AmmarPL/Outdoor-Air-Pollution/Presentation/Inverse_Distance_Plots/Final/NO2.JPG

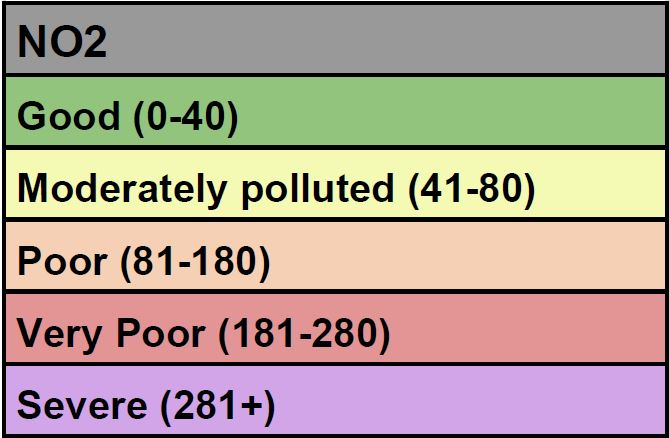
Presentation/Inverse_Distance_Plots/Final/NO2.JPG
