AmmarPL/Outdoor-Air-Pollution/Circuit/Circuit_Diagram.png

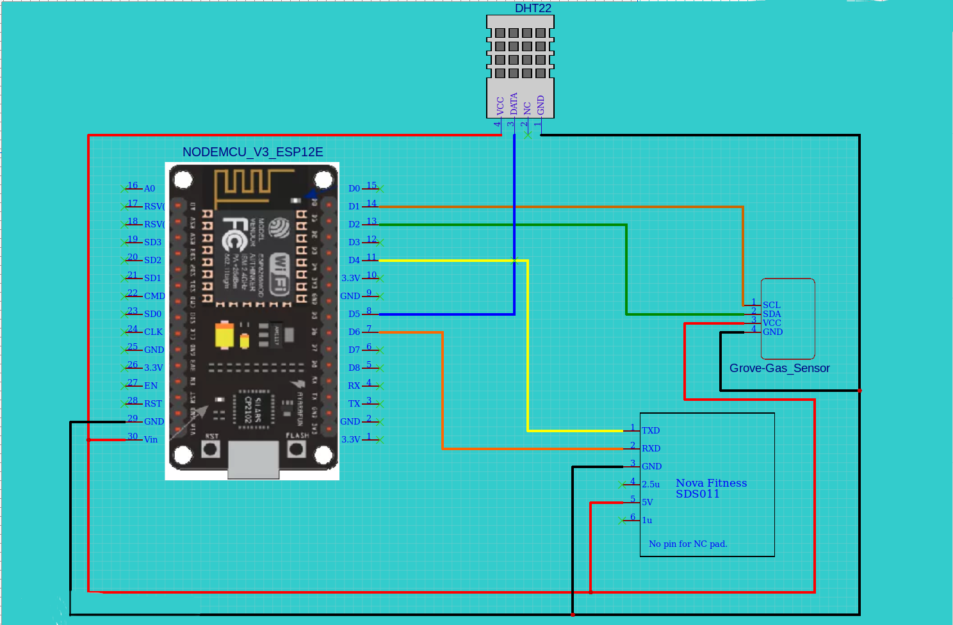
Circuit/Circuit_Diagram.png
