AmmarPL/Outdoor-Air-Pollution/Presentation/.picasaoriginals/Map.jpg

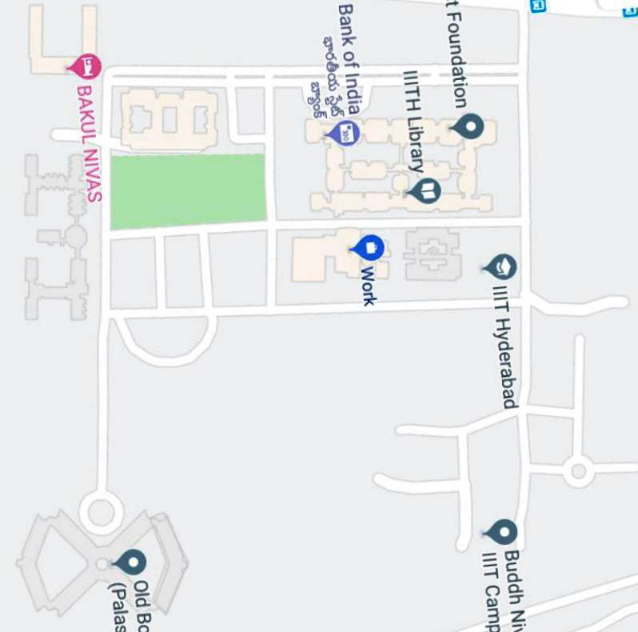
Presentation/.picasaoriginals/Map.jpg
