AmmarPL/Outdoor-Air-Pollution/Presentation/Comparison_Plots/CO.png

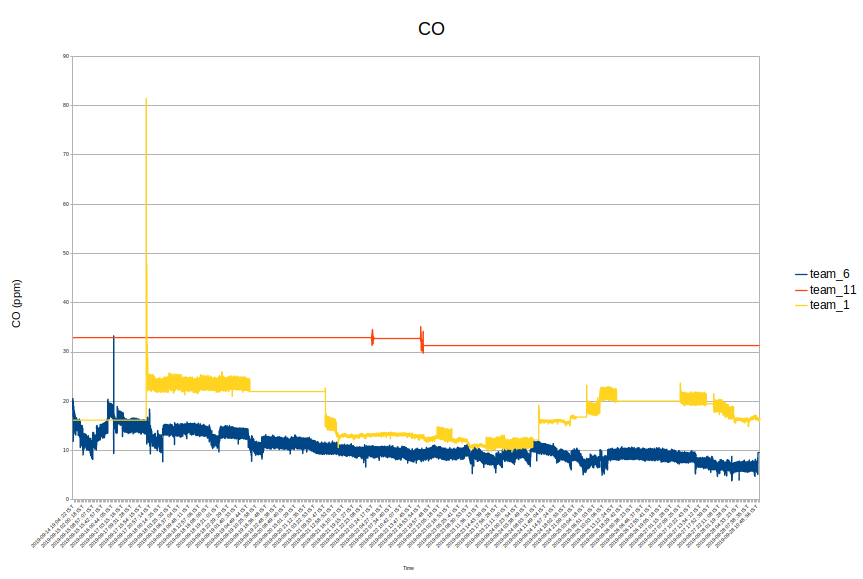
Presentation/Comparison_Plots/CO.png
