AmmarPL/Outdoor-Air-Pollution/Presentation/Comparison_Plots/Humidity.png

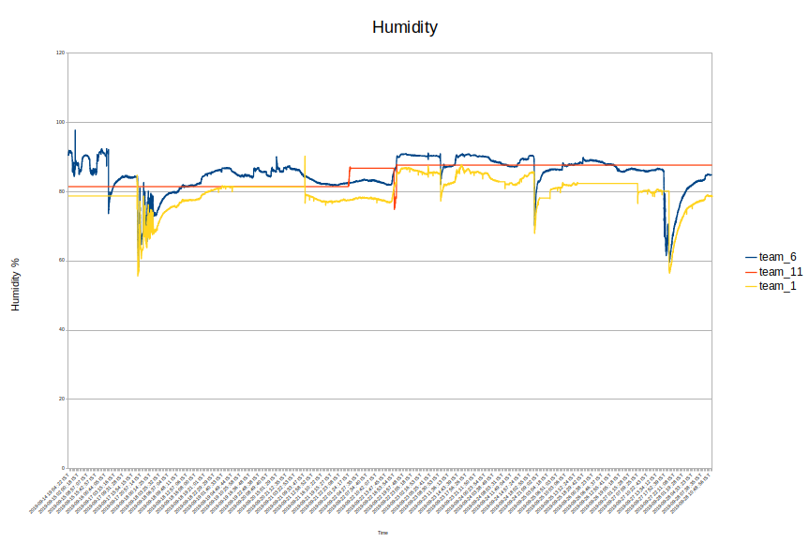
Presentation/Comparison_Plots/Humidity.png
