AmmarPL/Outdoor-Air-Pollution/Presentation/Comparison_Plots/NH3.png

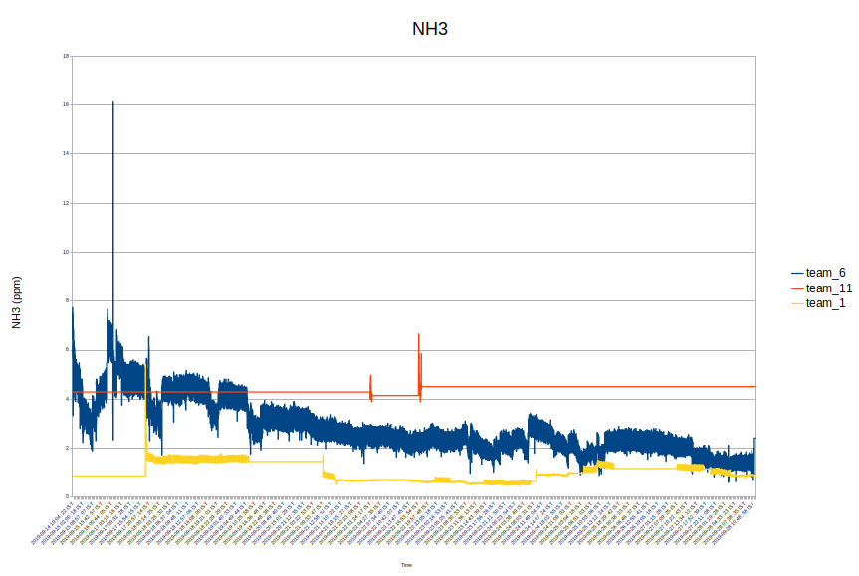
Presentation/Comparison_Plots/NH3.png
