AmmarPL/Outdoor-Air-Pollution/Presentation/Comparison_Plots/NO2.png

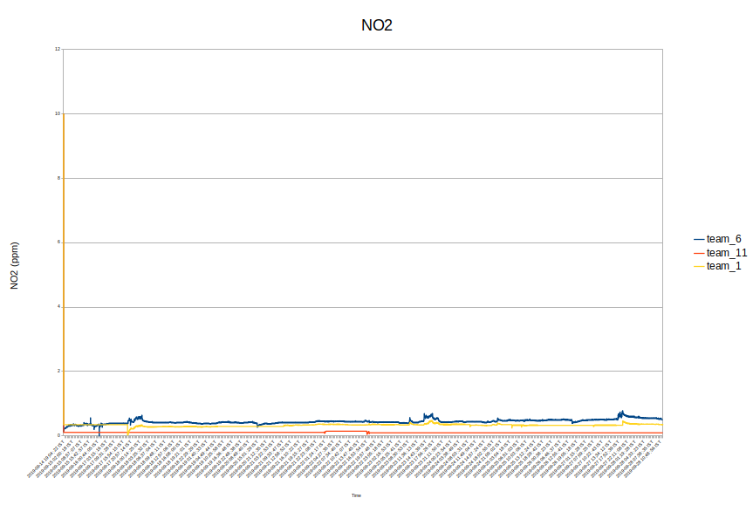
Presentation/Comparison_Plots/NO2.png
