AmmarPL/Outdoor-Air-Pollution/Presentation/Comparison_Plots/Pm25.png

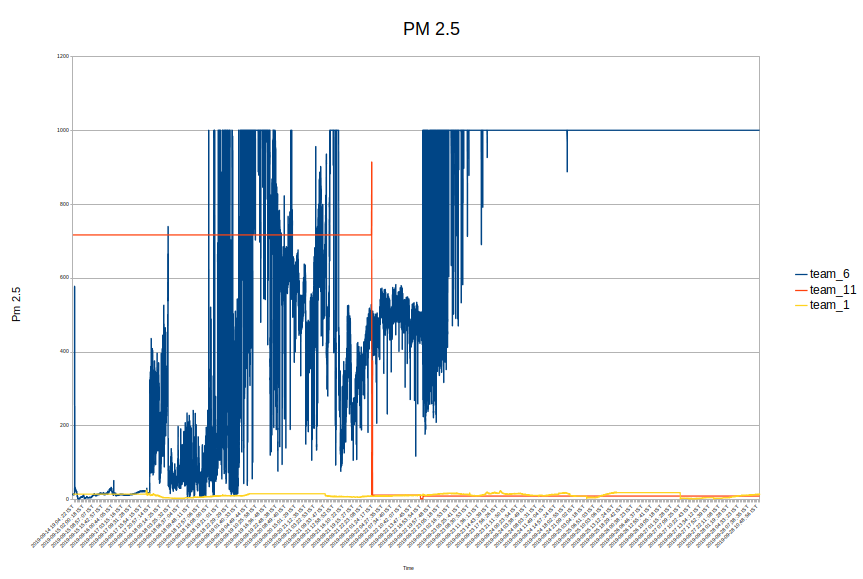
Presentation/Comparison_Plots/Pm25.png
