AmmarPL/Outdoor-Air-Pollution/Presentation/Inverse_Distance_Plots/Final/co.png

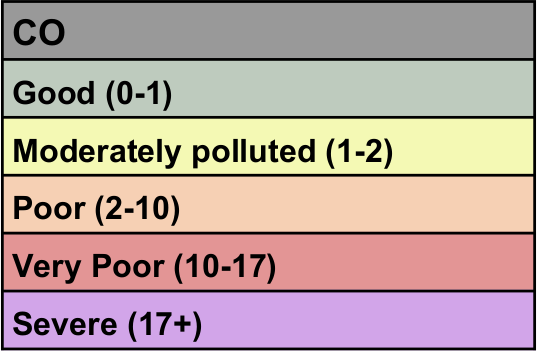
Presentation/Inverse_Distance_Plots/Final/co.png
