AmmarPL/Outdoor-Air-Pollution/Presentation/Inverse_Distance_Plots/Final/COfinal.png

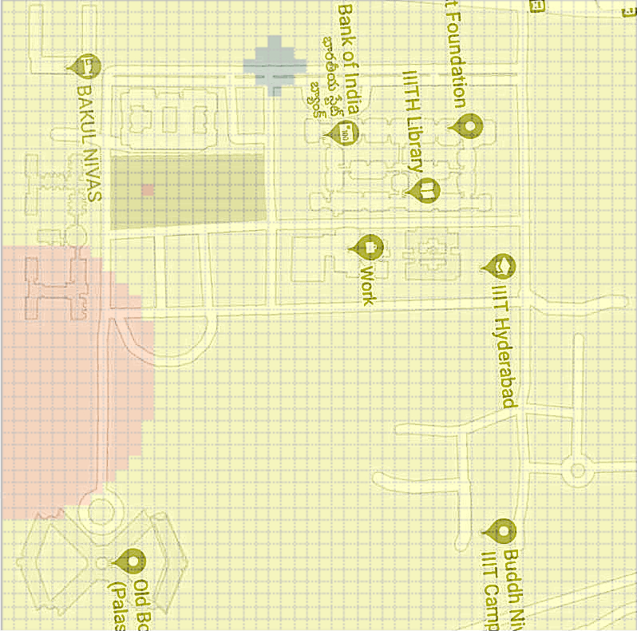
Presentation/Inverse_Distance_Plots/Final/COfinal.png
