AmmarPL/Outdoor-Air-Pollution/Presentation/Inverse_Distance_Plots/Final/nh3.JPG

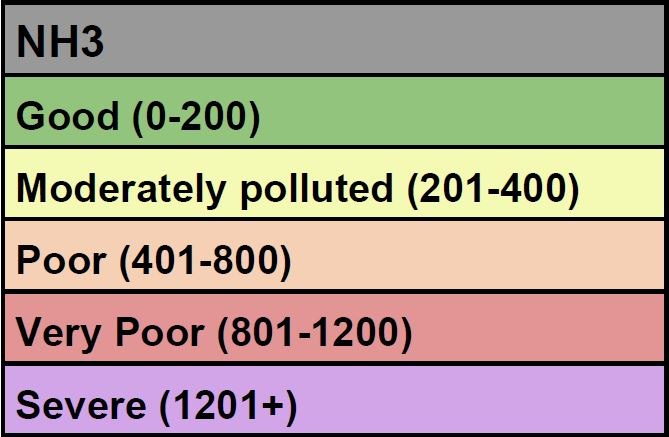
Presentation/Inverse_Distance_Plots/Final/nh3.JPG
