AmmarPL/Outdoor-Air-Pollution/Presentation/Inverse_Distance_Plots/Final/NH3final.png

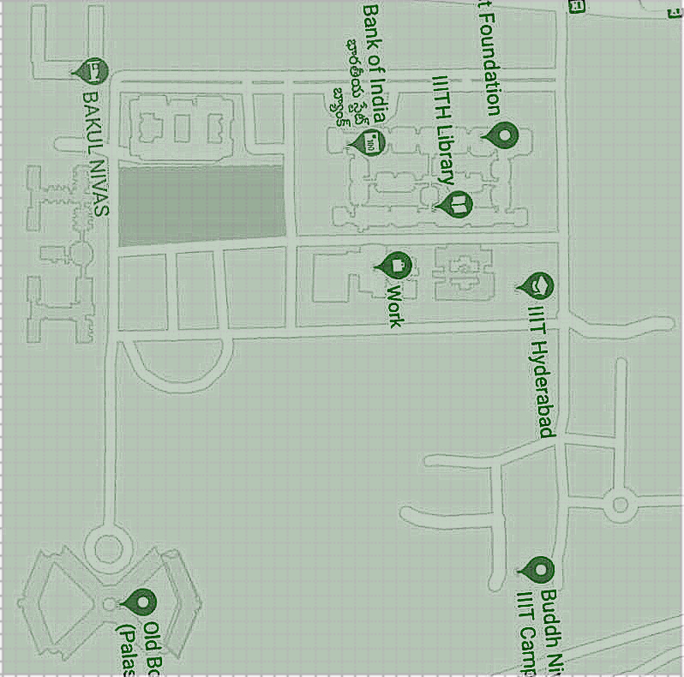
Presentation/Inverse_Distance_Plots/Final/NH3final.png
