AmmarPL/Outdoor-Air-Pollution/Presentation/Inverse_Distance_Plots/Final/PM10final.png

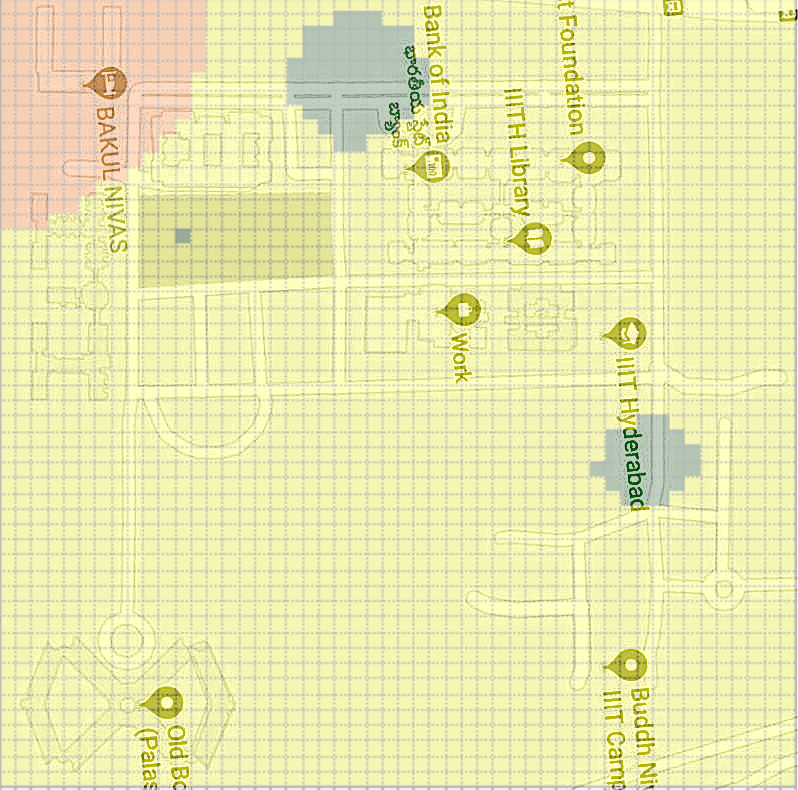
Presentation/Inverse_Distance_Plots/Final/PM10final.png
