AmmarPL/Outdoor-Air-Pollution/Presentation/Inverse_Distance_Plots/Final/PM25final.png

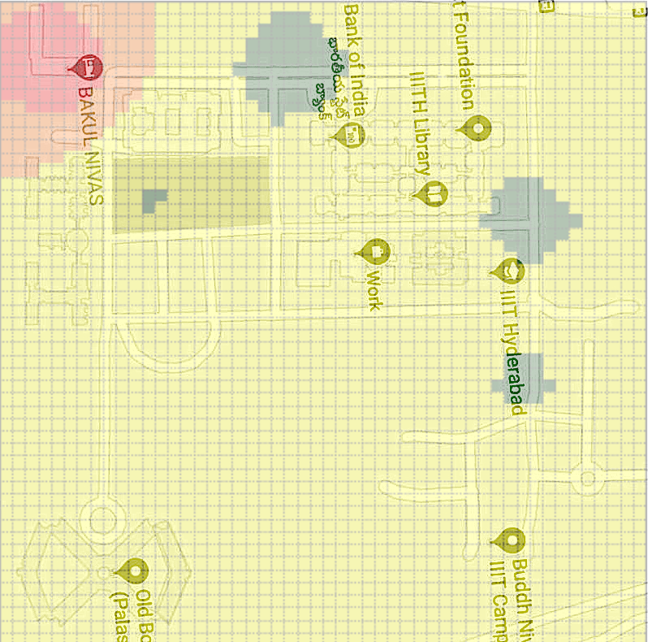
Presentation/Inverse_Distance_Plots/Final/PM25final.png
