AmmarPL/Outdoor-Air-Pollution/Presentation/Inverse_Distance_Plots/RAW/CO.png

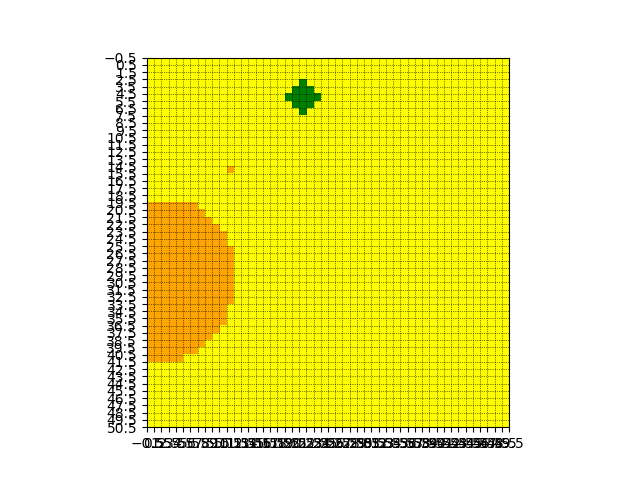
Presentation/Inverse_Distance_Plots/RAW/CO.png
