AmmarPL/Outdoor-Air-Pollution/Presentation/Inverse_Distance_Plots/RAW/NH3.png

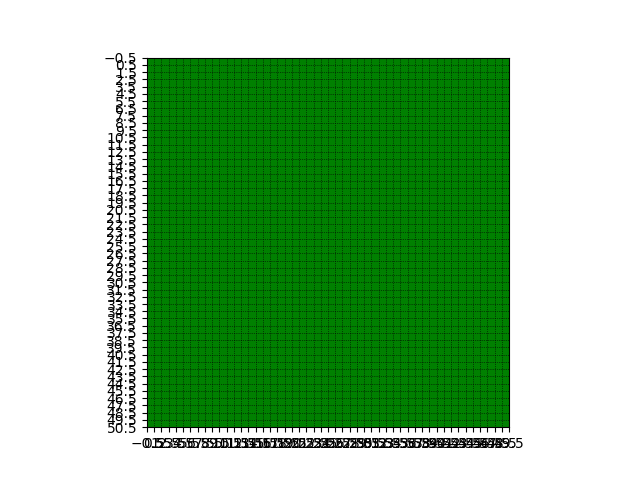
Presentation/Inverse_Distance_Plots/RAW/NH3.png
