AmmarPL/Outdoor-Air-Pollution/Presentation/Inverse_Distance_Plots/RAW/PM10.png

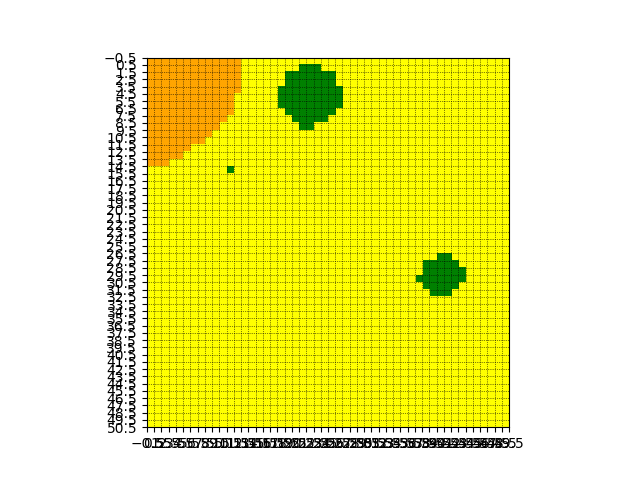
Presentation/Inverse_Distance_Plots/RAW/PM10.png
