AmmarPL/Outdoor-Air-Pollution/Presentation/Locations/Legend.JPG

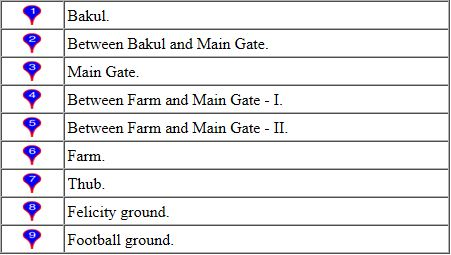
Presentation/Locations/Legend.JPG
