AmmarPL/Outdoor-Air-Pollution/Presentation/Locations/Map_Edit.jpg

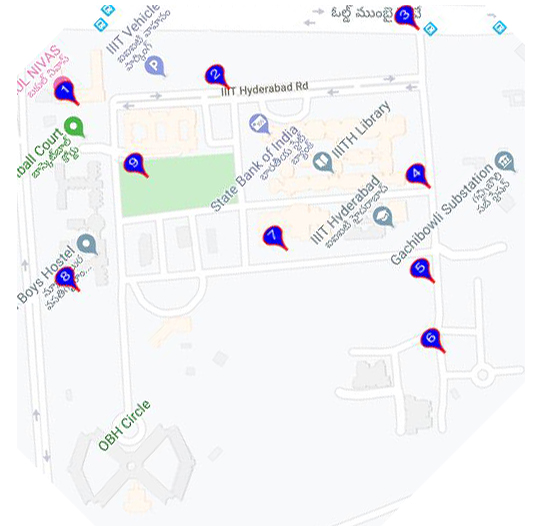
Presentation/Locations/Map_Edit.jpg
