AmmarPL/Outdoor-Air-Pollution/Presentation/Node_Comparison/CO_1_2.png

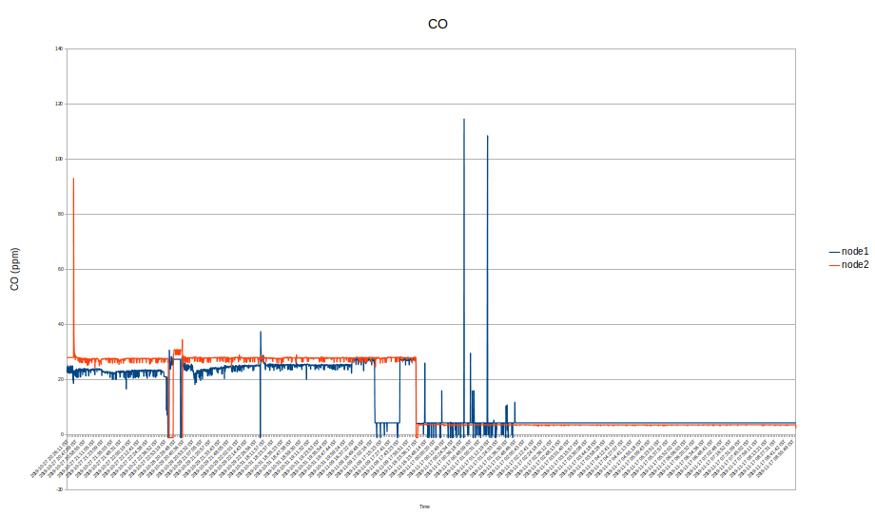
Presentation/Node_Comparison/CO_1_2.png
