AmmarPL/Outdoor-Air-Pollution/Presentation/Node_Comparison/Humdity_1_2.png

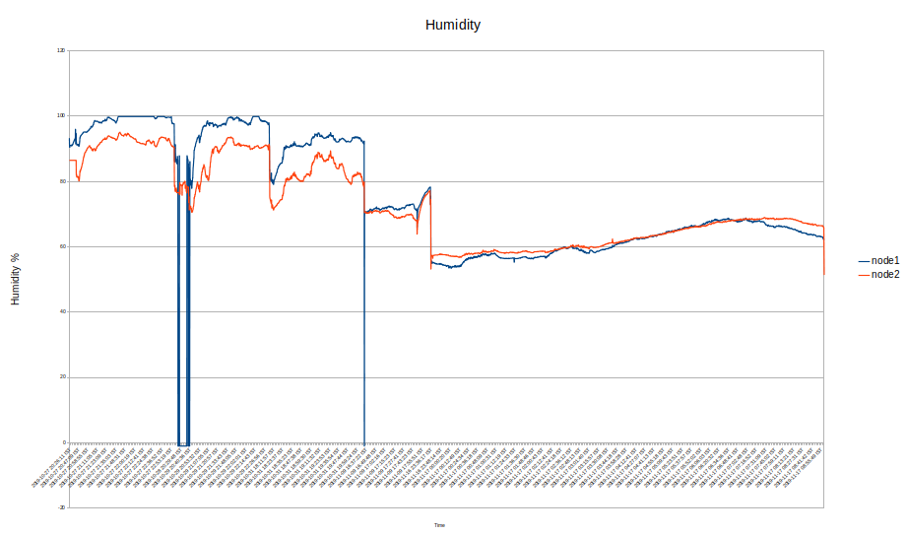
Presentation/Node_Comparison/Humdity_1_2.png
