AmmarPL/Outdoor-Air-Pollution/Presentation/Node_Comparison/NH3_1_2.png

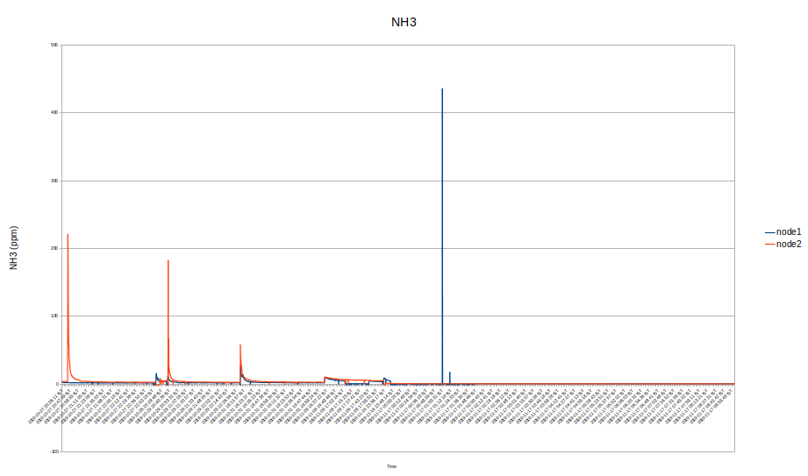
Presentation/Node_Comparison/NH3_1_2.png
