AmmarPL/Outdoor-Air-Pollution/Presentation/Node_Comparison/NO2_1_2.png

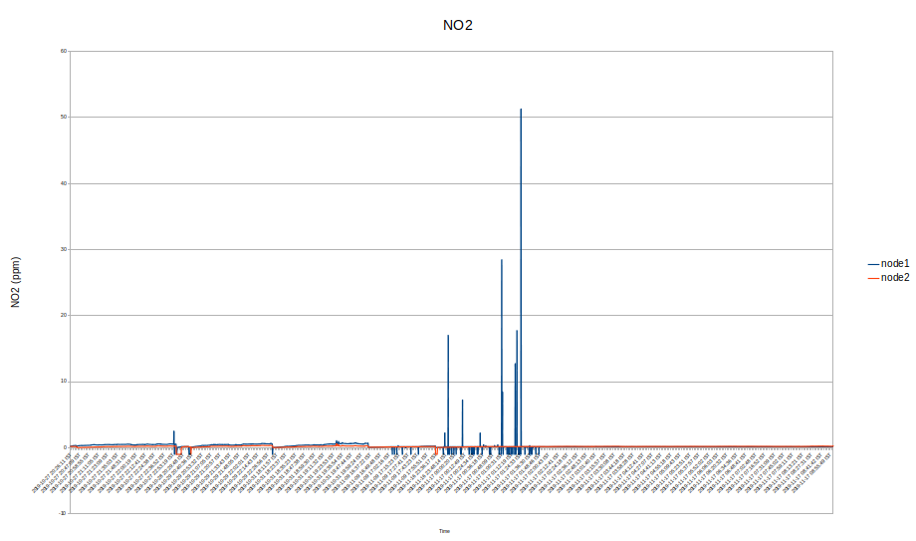
Presentation/Node_Comparison/NO2_1_2.png
