AmmarPL/Outdoor-Air-Pollution/Presentation/Node_Comparison/PM10_1_2.png

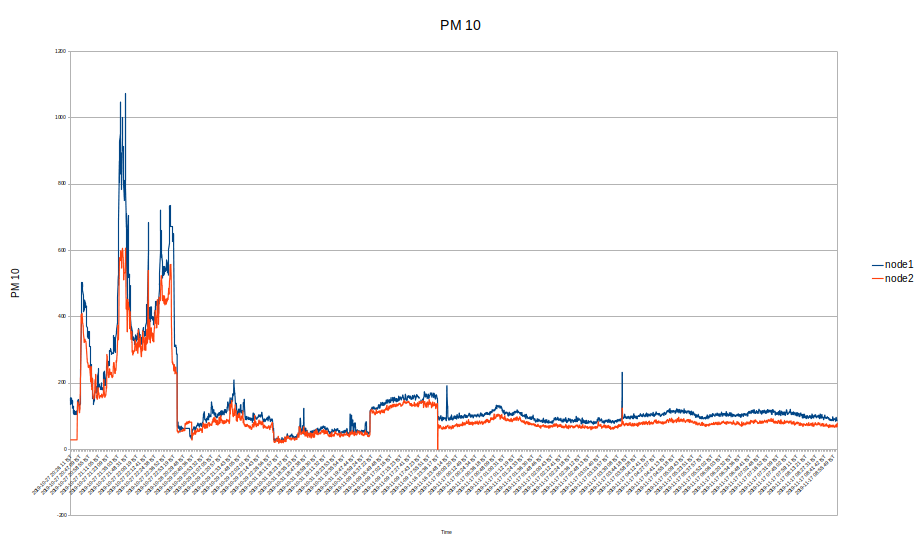
Presentation/Node_Comparison/PM10_1_2.png
