AmmarPL/Outdoor-Air-Pollution/Presentation/Node_Comparison/Temperature_1_2.png

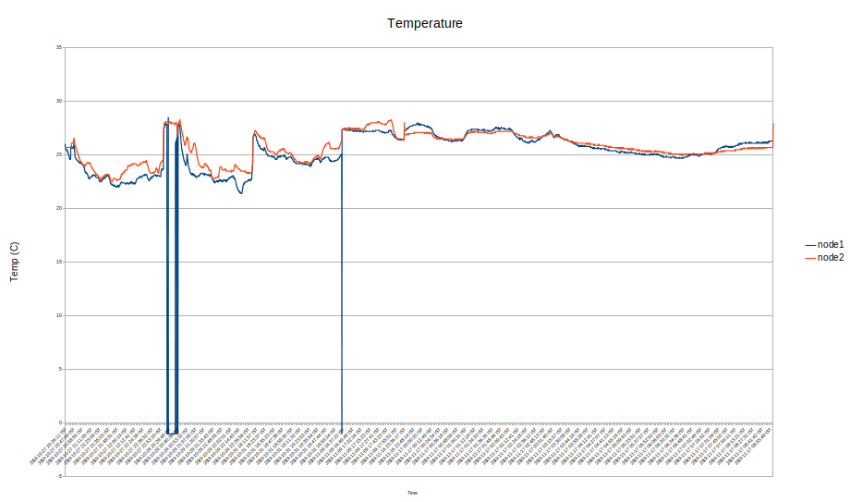
Presentation/Node_Comparison/Temperature_1_2.png
