AmmarPL/Outdoor-Air-Pollution/Presentation/Team6_Plots/H2.png

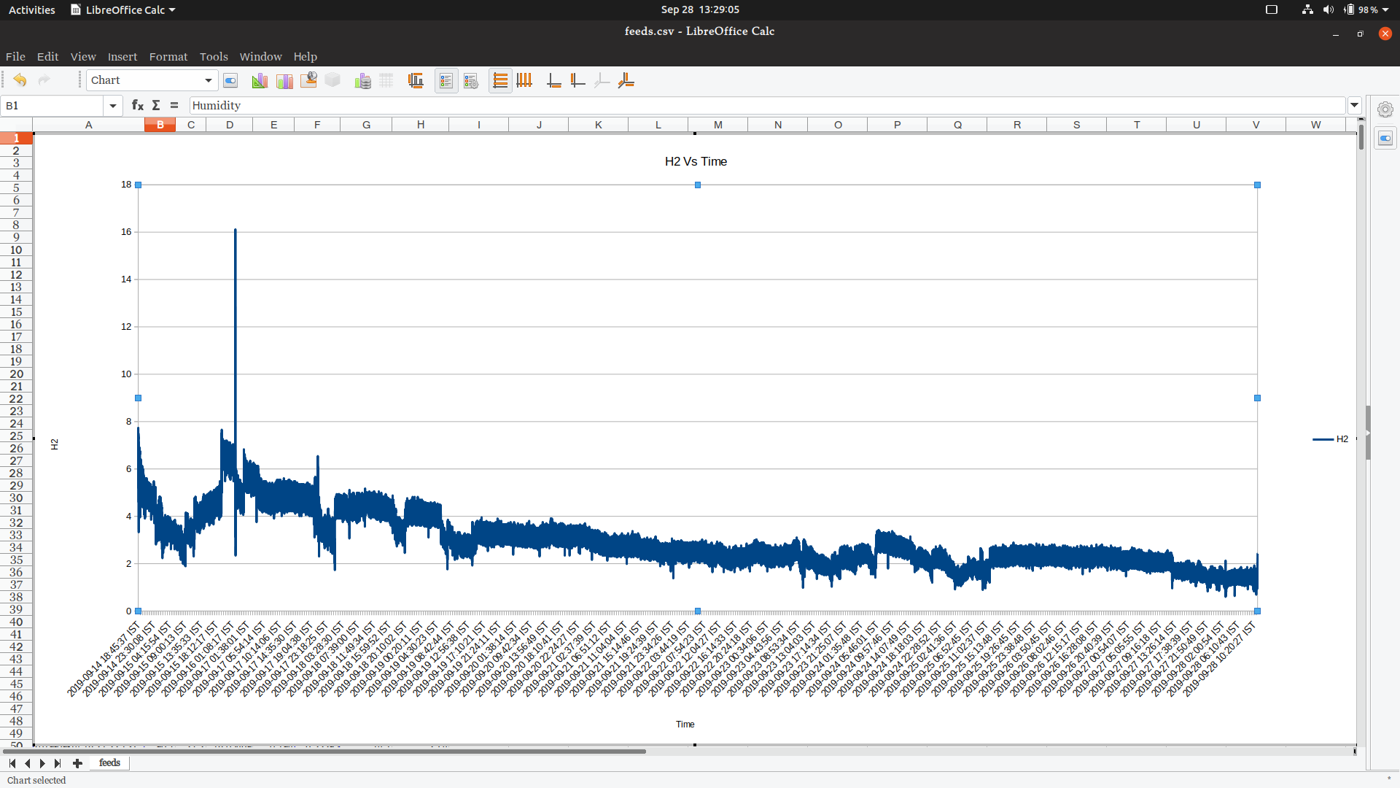
Presentation/Team6_Plots/H2.png
