AmmarPL/Outdoor-Air-Pollution/Presentation/Team6_Plots/Humidity.png

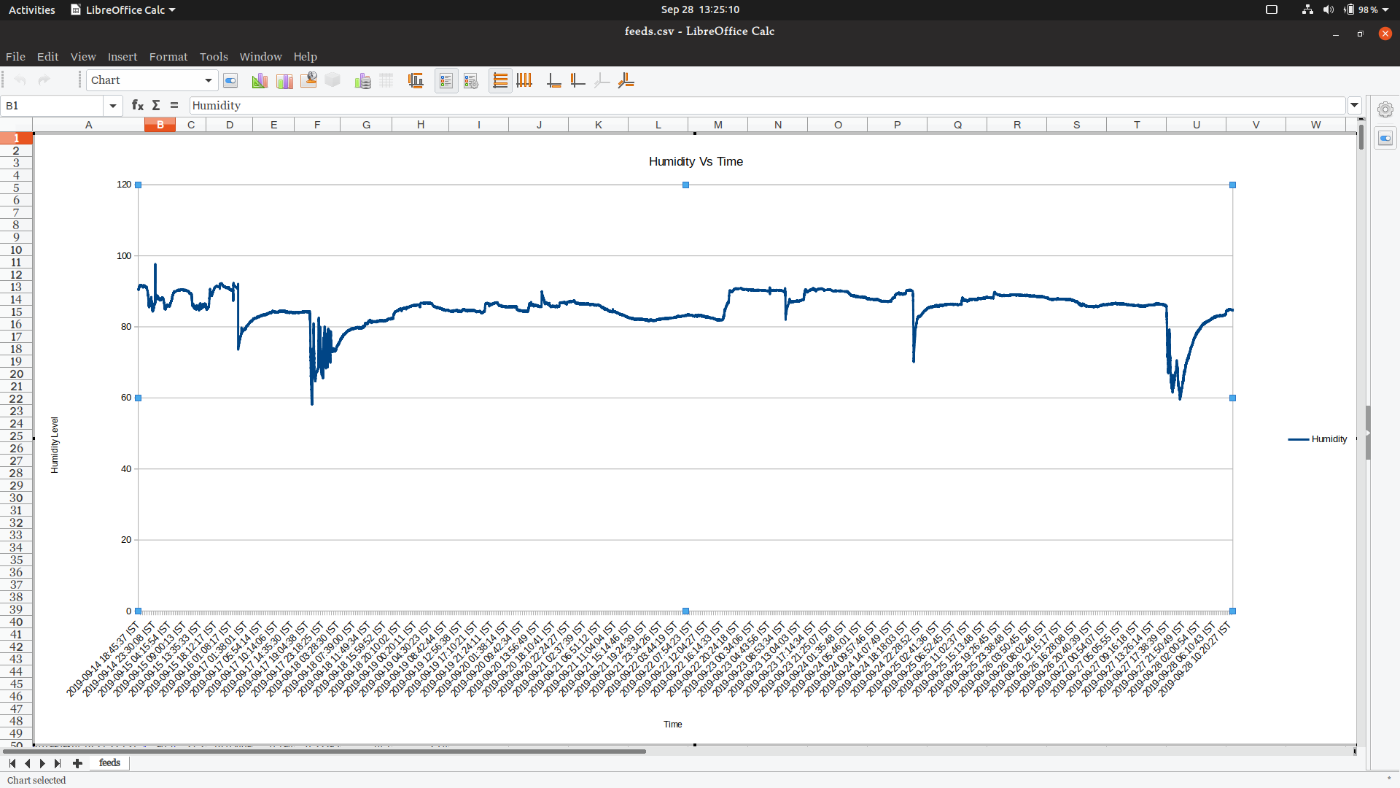
Presentation/Team6_Plots/Humidity.png
