AmmarPL/Outdoor-Air-Pollution/Presentation/Team6_Plots/NO2.png

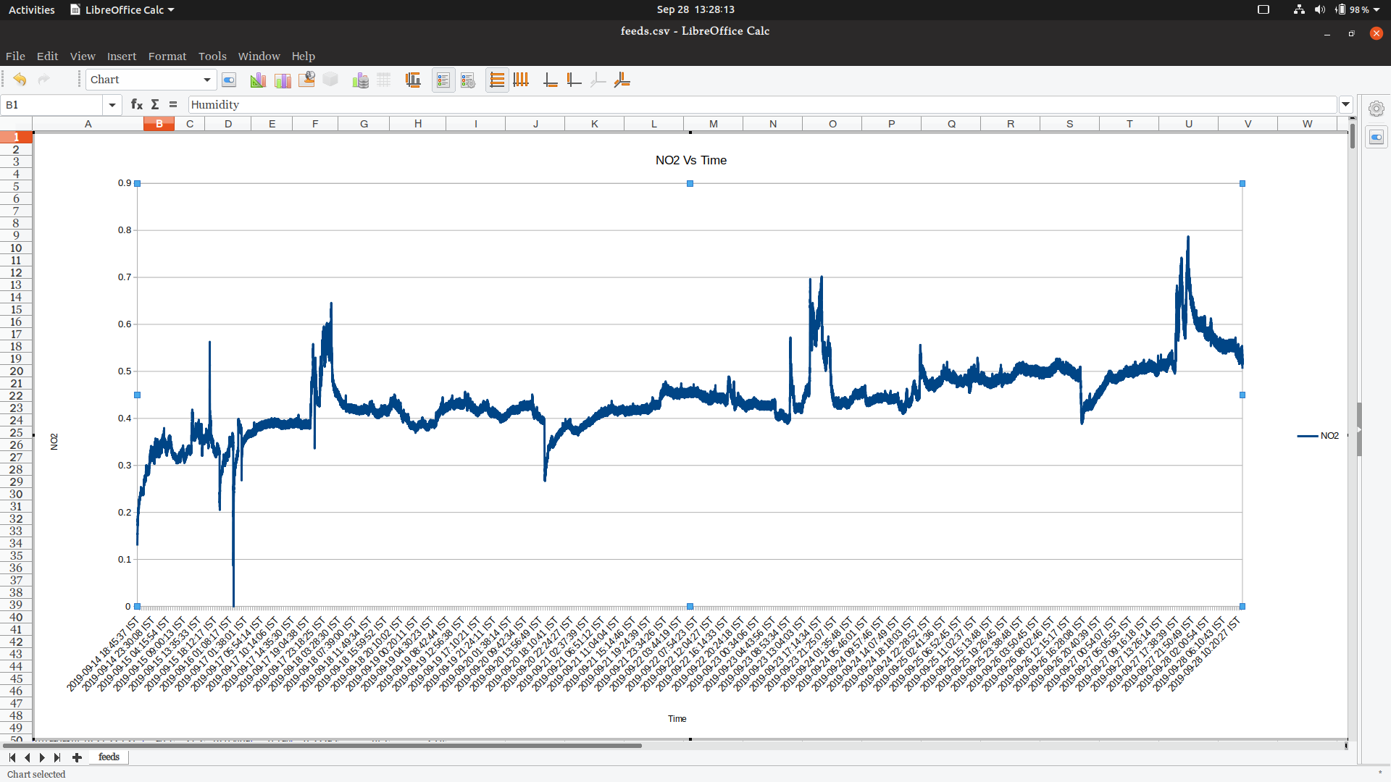
Presentation/Team6_Plots/NO2.png
