AmmarPL/Outdoor-Air-Pollution/Presentation/Team6_Plots/PM10.png

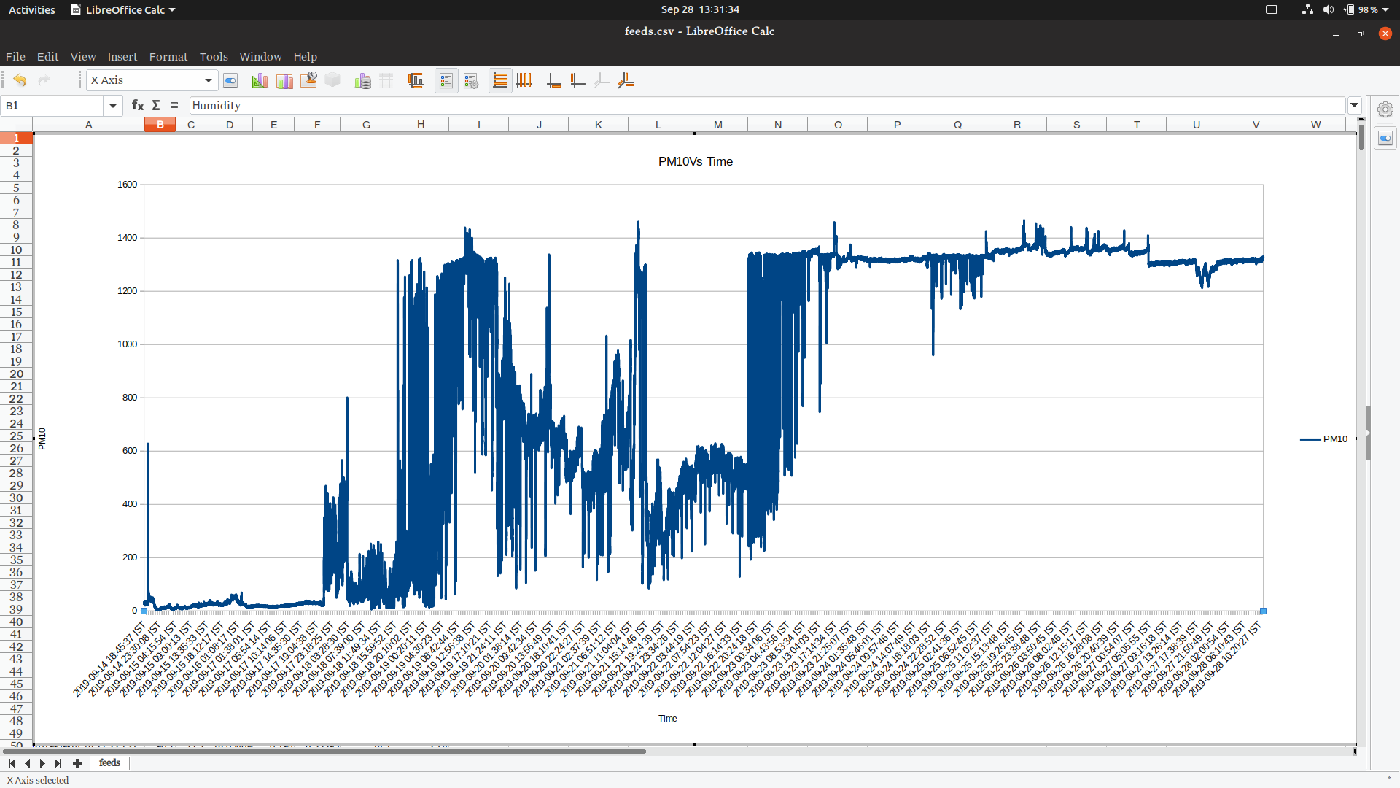
Presentation/Team6_Plots/PM10.png
