AmmarPL/Outdoor-Air-Pollution/Presentation/Team6_Plots/PM25.png

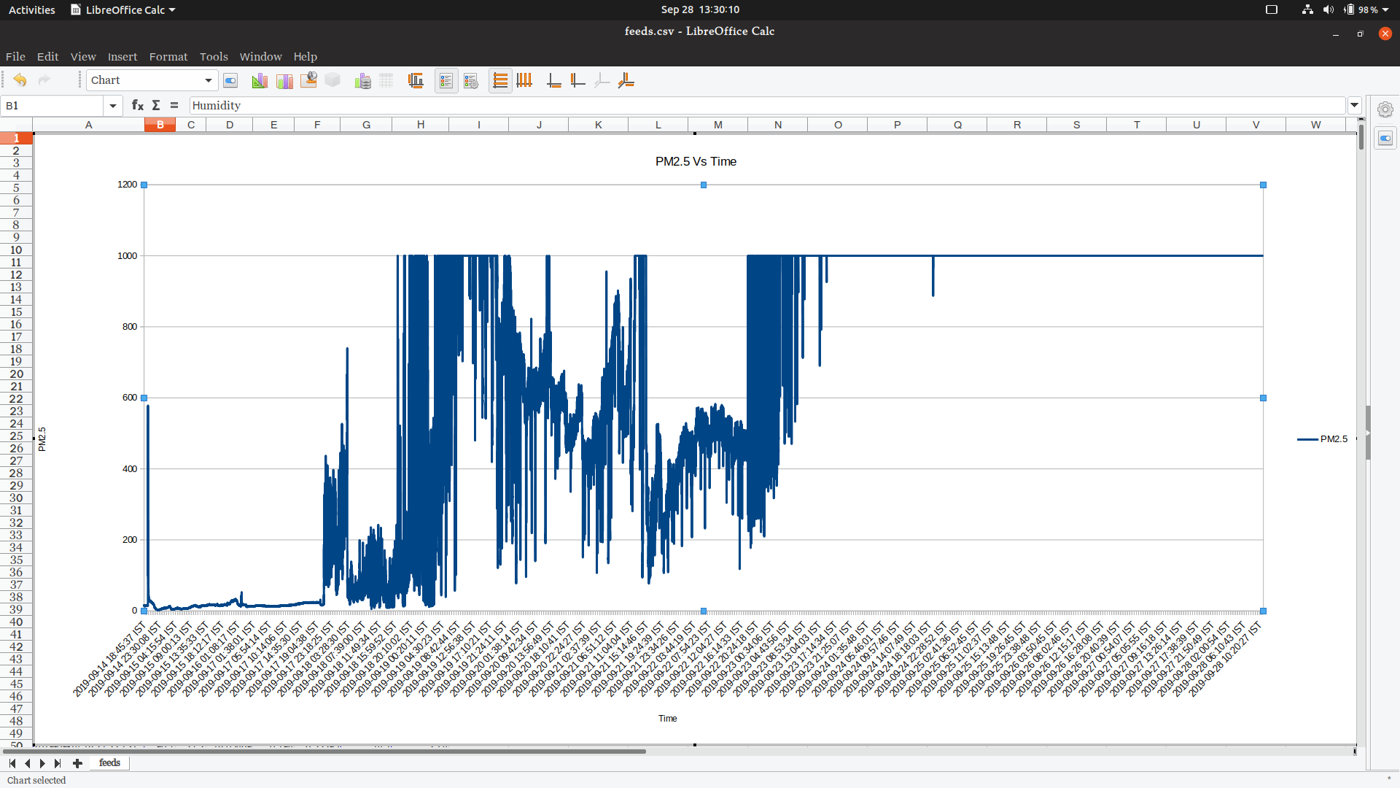
Presentation/Team6_Plots/PM25.png
