AmmarPL/Outdoor-Air-Pollution/Presentation/Team6_Plots/Temperature.png

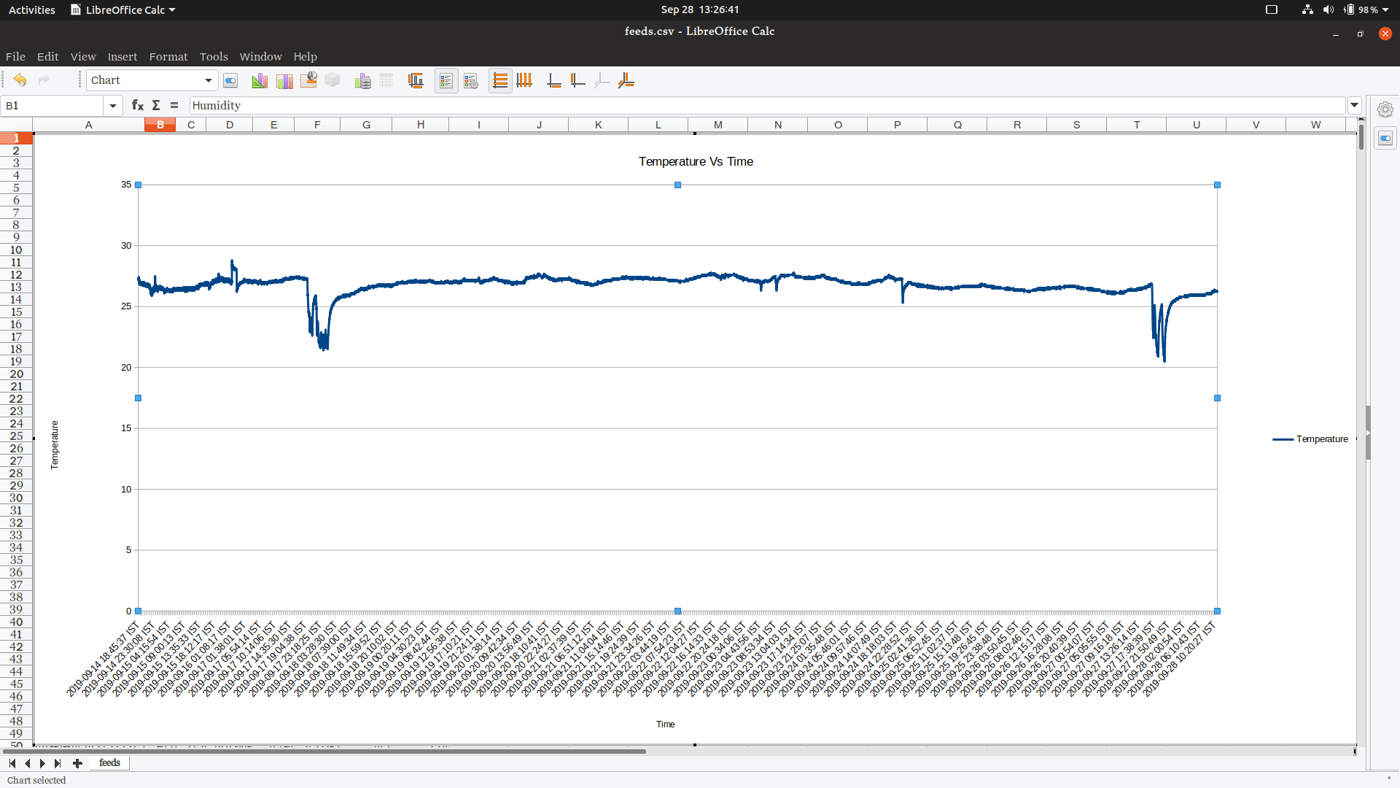
Presentation/Team6_Plots/Temperature.png
